mongoose-os-apps/12V-8Port-Switch/src/main.c

#include "channel.h"
#include "current.h"
#include "mgos.h"
#include "rpc.h"

enum mgos_app_init_result mgos_app_init(void) {
  channel_init();
  current_init();
  rpc_init();
  return MGOS_APP_INIT_SUCCESS;
}
